HybridBodyLab/wet-spinning-machine/3d_models_stl/ShaftSleeve.stl

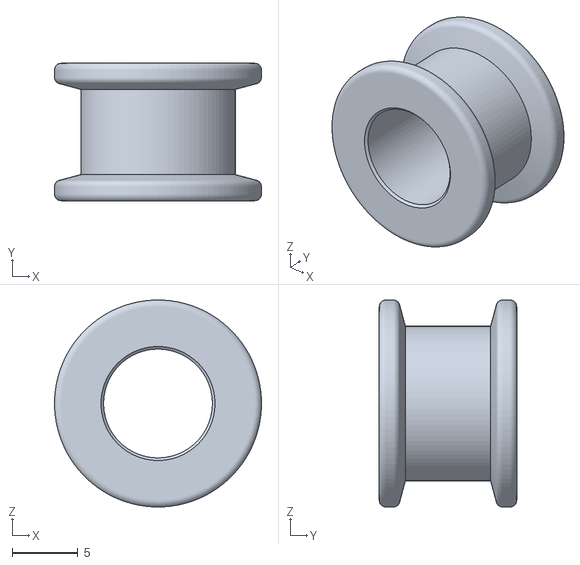
[picture p15: CAD file, 2025-04-15]
3d_models_stl/ShaftSleeve.stl
15.8 x 10.5 x 15.8
