HybridBodyLab/wet-spinning-machine/3d_models_stl/Roller.stl

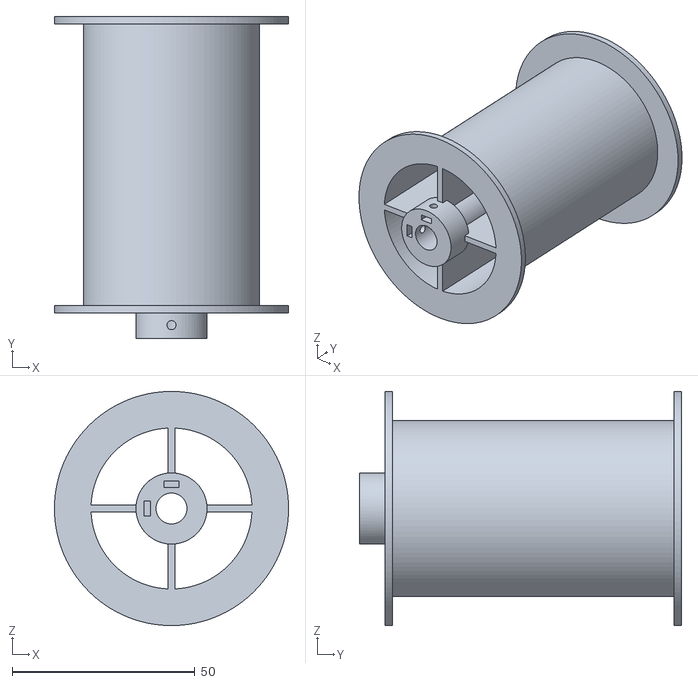
[picture p16: CAD file, 2025-04-15]
3d_models_stl/Roller.stl
64.0 x 88.0 x 64.0
