HybridBodyLab/wet-spinning-machine/3d_models_stl/WashBath.stl

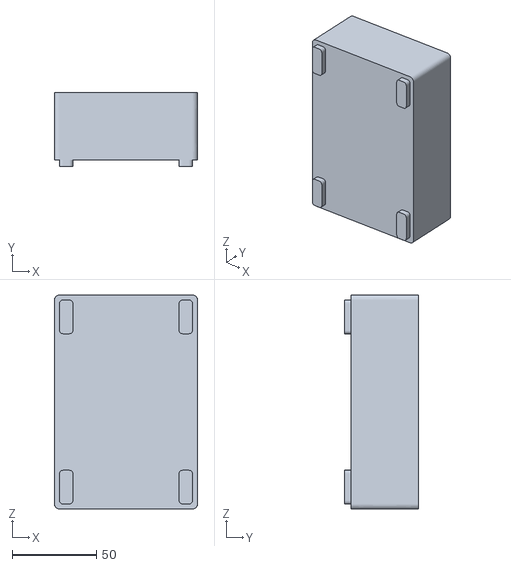
[picture p17: CAD file, 2025-04-15]
3d_models_stl/WashBath.stl
85.0 x 44.0 x 127.0
