HybridBodyLab/wet-spinning-machine/3d_models_stl/Post.stl

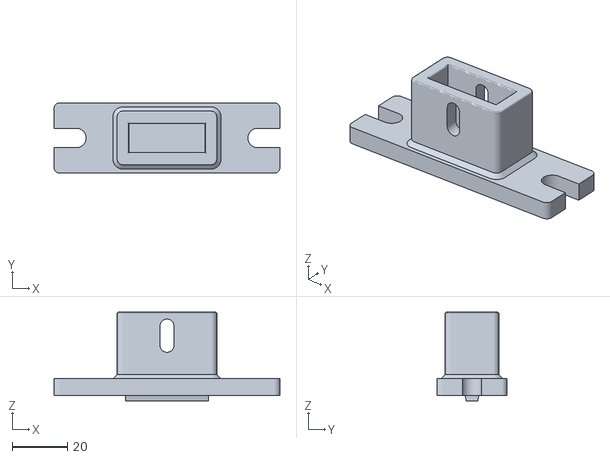
[picture p18: CAD file, 2025-04-15]
3d_models_stl/Post.stl
81.6 x 25.4 x 32.0
