HybridBodyLab/wet-spinning-machine/3d_models_stl/SyringeMotorMount.stl

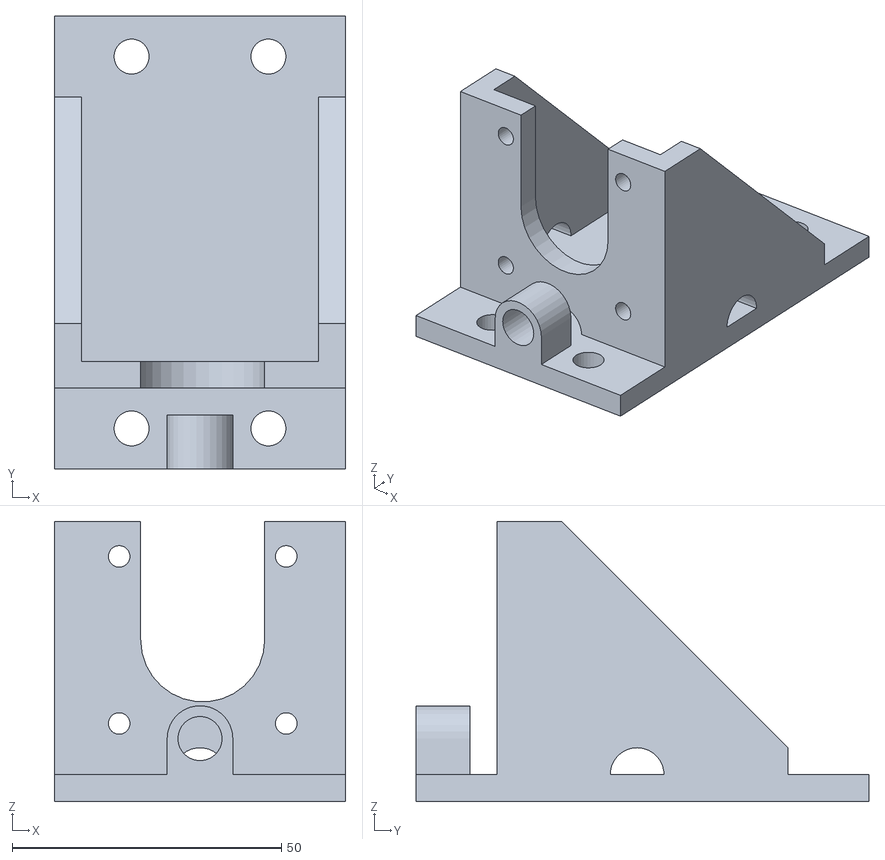
[picture p19: CAD file, 2025-04-15]
3d_models_stl/SyringeMotorMount.stl
54.0 x 84.0 x 52.0
