HybridBodyLab/wet-spinning-machine/3d_models_stl/SyringeHubHolder.stl

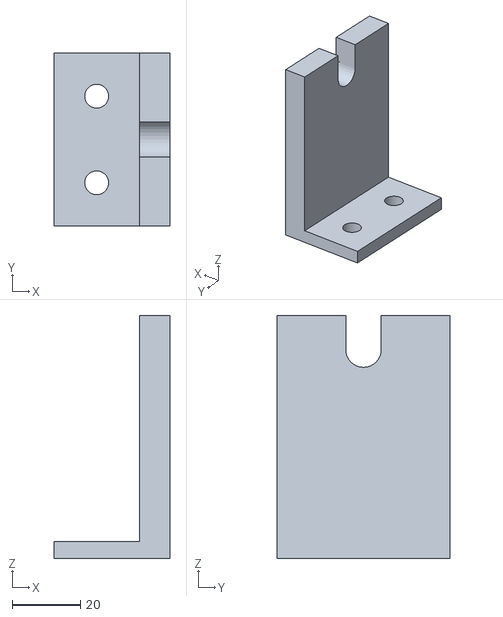
[picture p20: CAD file, 2025-04-15]
3d_models_stl/SyringeHubHolder.stl
34.0 x 50.8 x 71.2
