HybridBodyLab/wet-spinning-machine/3d_models_stl/CoagulationBath.stl

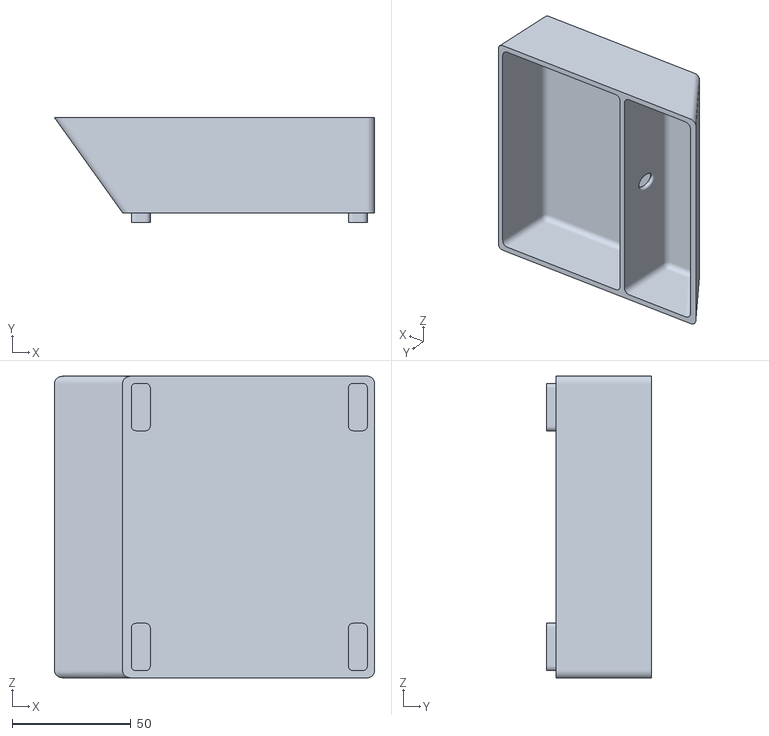
[picture p21: CAD file, 2025-04-15]
3d_models_stl/CoagulationBath.stl
134.7 x 44.0 x 127.0
